radrajith/ESE_323_PCB_Design/Datasheets/4 pin connector/╨┬╜¿╬─╝■╝╨/CCF20160824.jpg

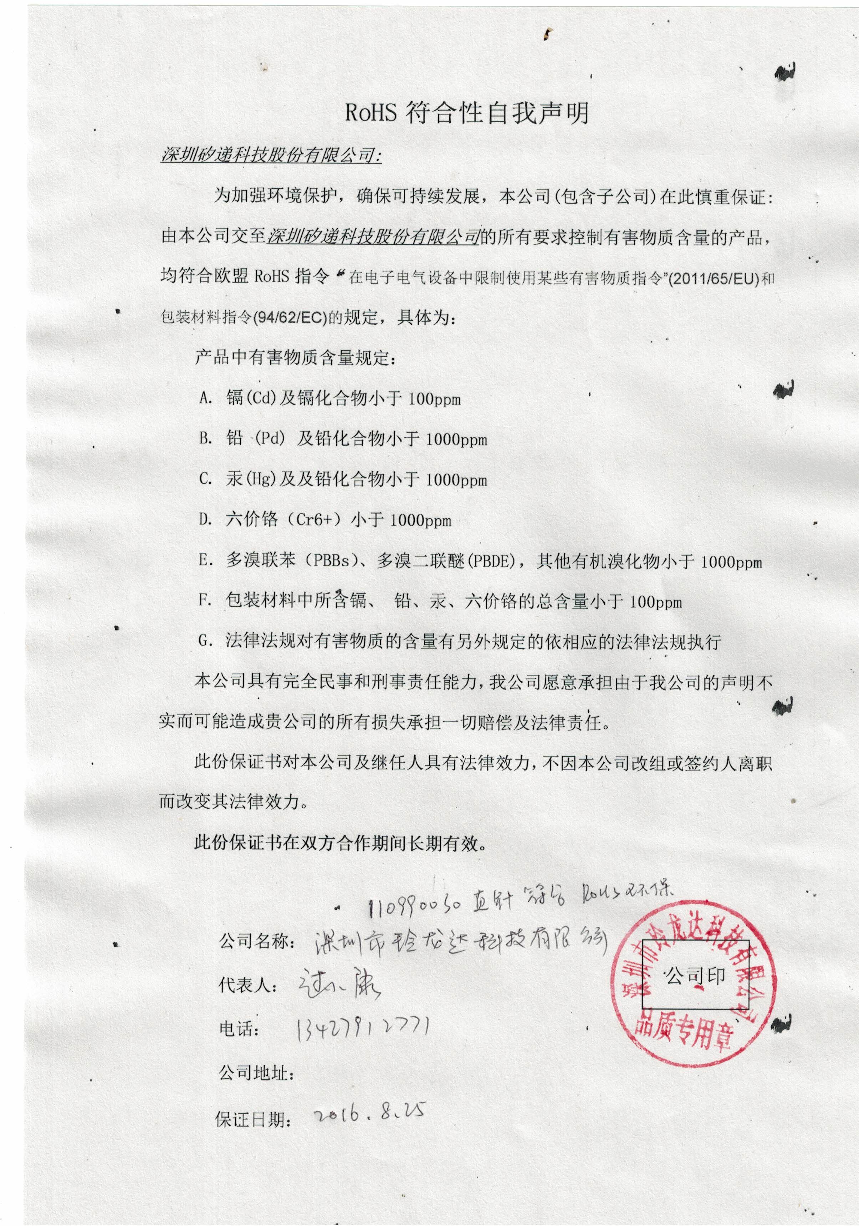
Datasheets/4 pin connector/╨┬╜¿╬─╝■╝╨/CCF20160824.jpg
