radrajith/ESE_323_PCB_Design/Pictures/4 terminal resistor.PNG

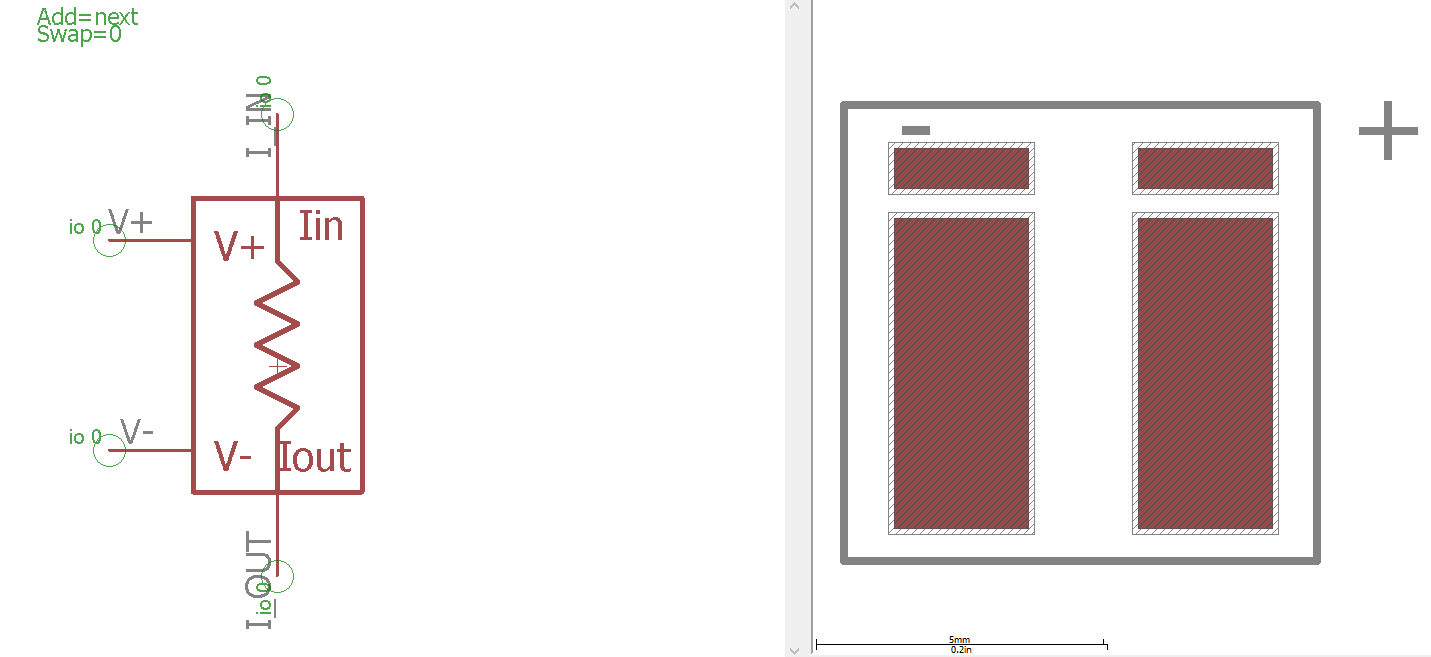
Pictures/4 terminal resistor.PNG
