radrajith/ESE_323_PCB_Design/Pictures/Atxmega/atxmega32.PNG

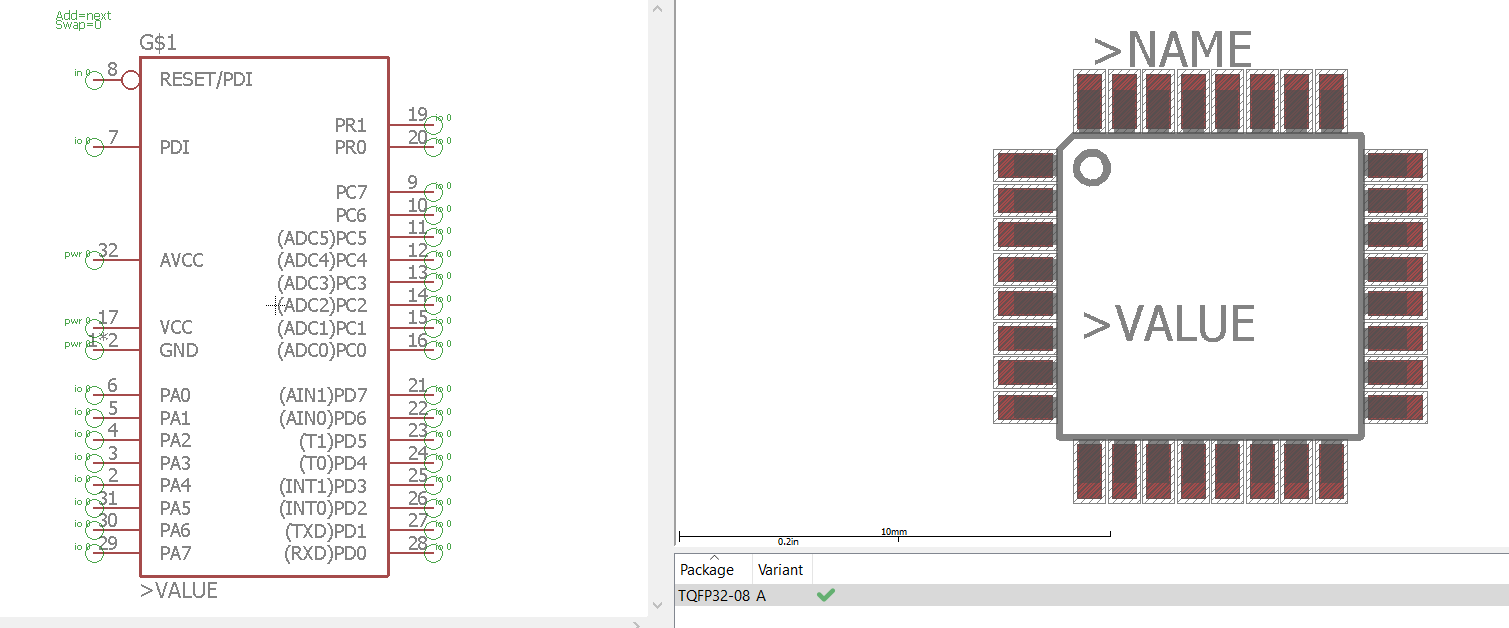
Pictures/Atxmega/atxmega32.PNG
