radrajith/ESE_323_PCB_Design/Pictures/Atxmega/pinouts.PNG

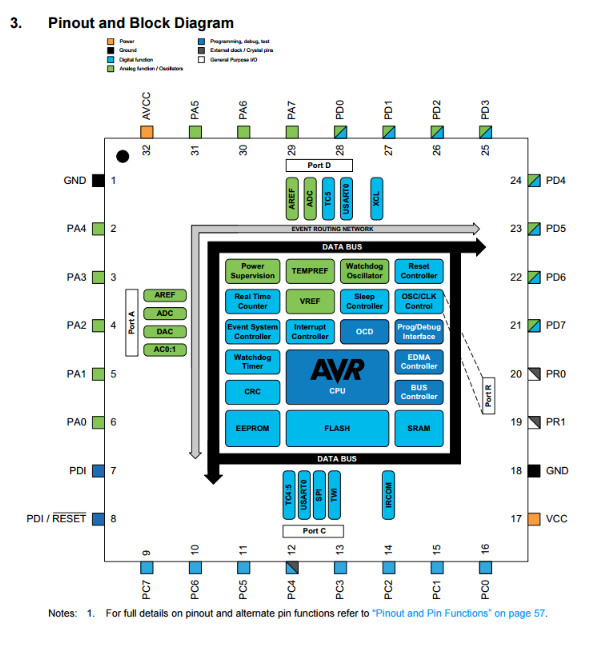
Pictures/Atxmega/pinouts.PNG
