radrajith/ESE_323_PCB_Design/Pictures/banana plug.PNG

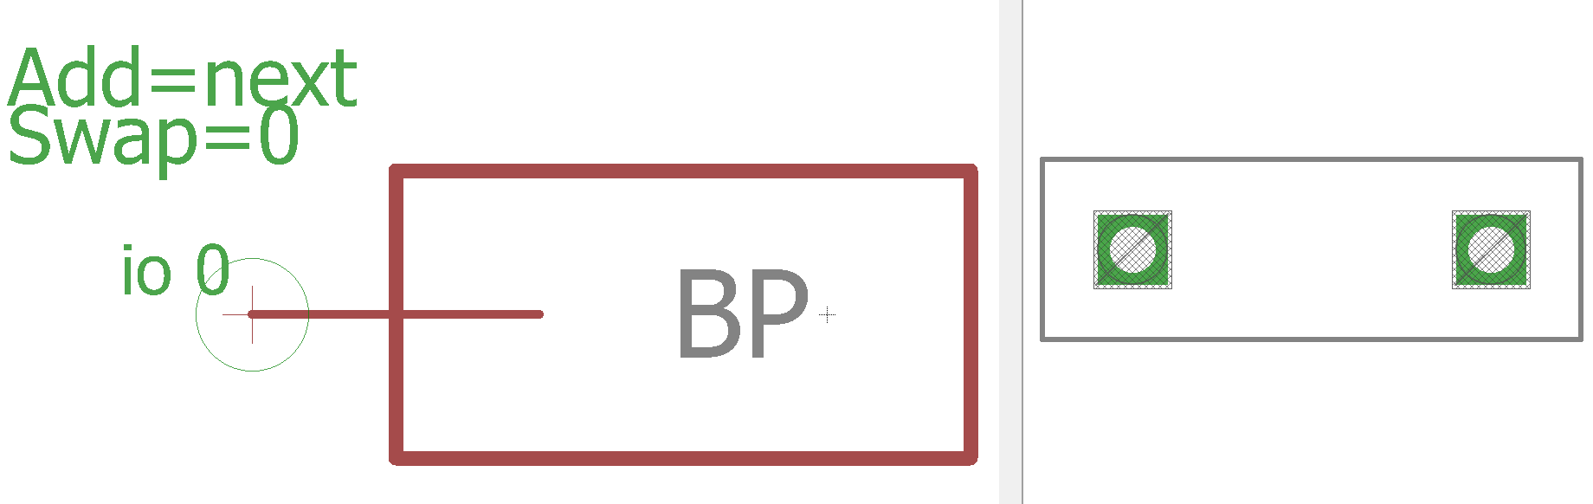
Pictures/banana plug.PNG
