radrajith/ESE_323_PCB_Design/Pictures/battery_case_Cad.PNG

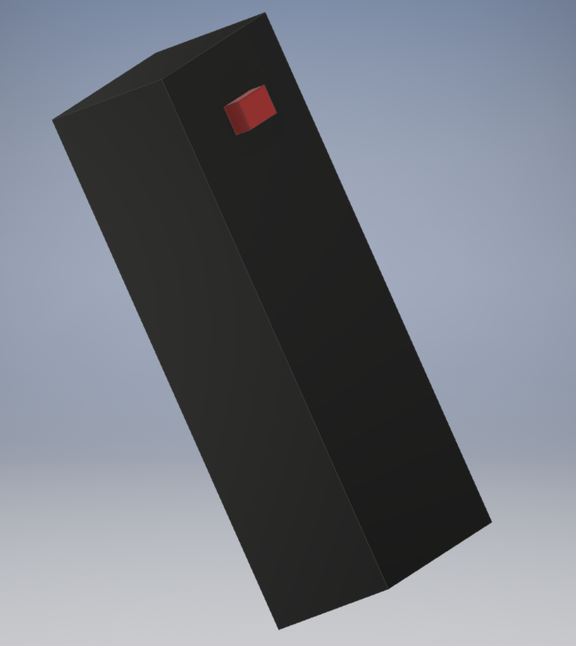
Pictures/battery_case_Cad.PNG
