radrajith/ESE_323_PCB_Design/Pictures/bottom_case.PNG

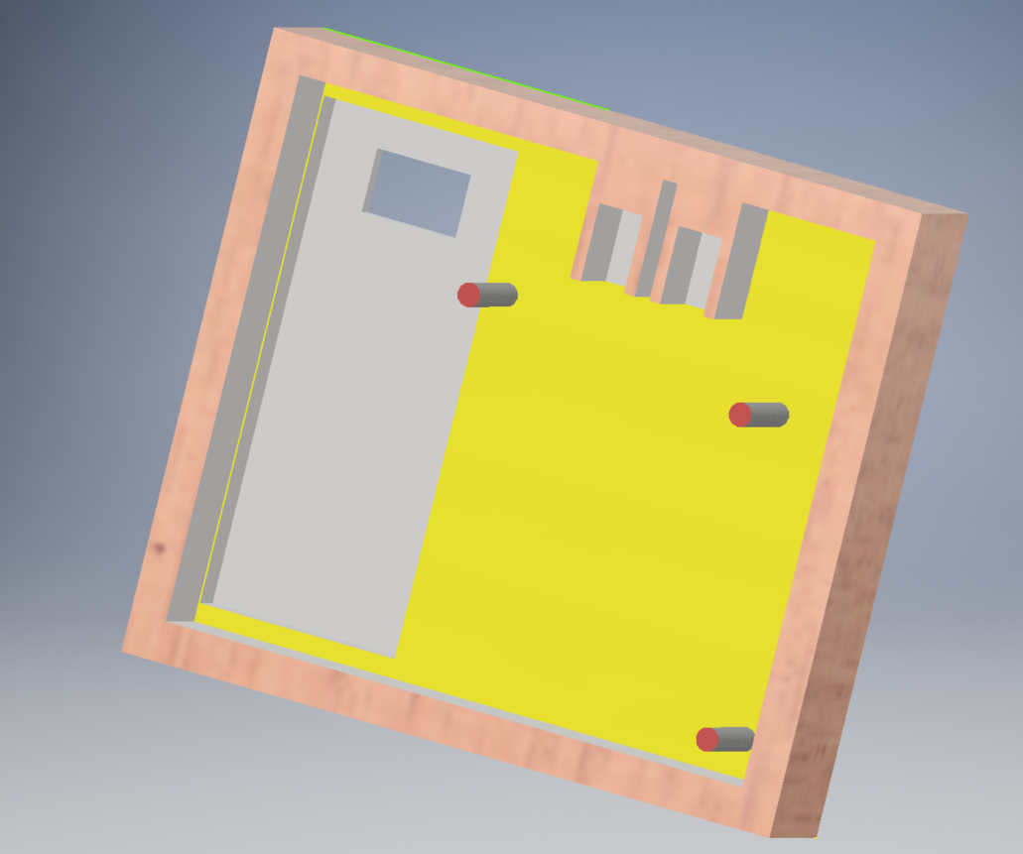
Pictures/bottom_case.PNG
