radrajith/ESE_323_PCB_Design/Pictures/button_press.PNG

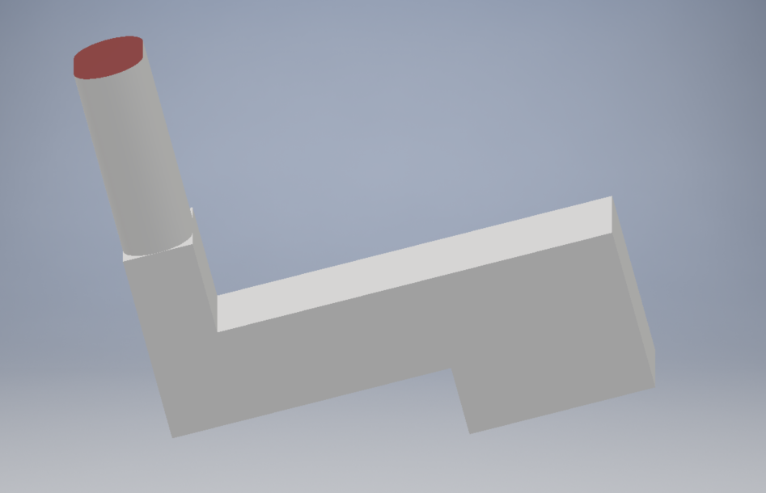
Pictures/button_press.PNG
