radrajith/ESE_323_PCB_Design/Pictures/jtag.PNG

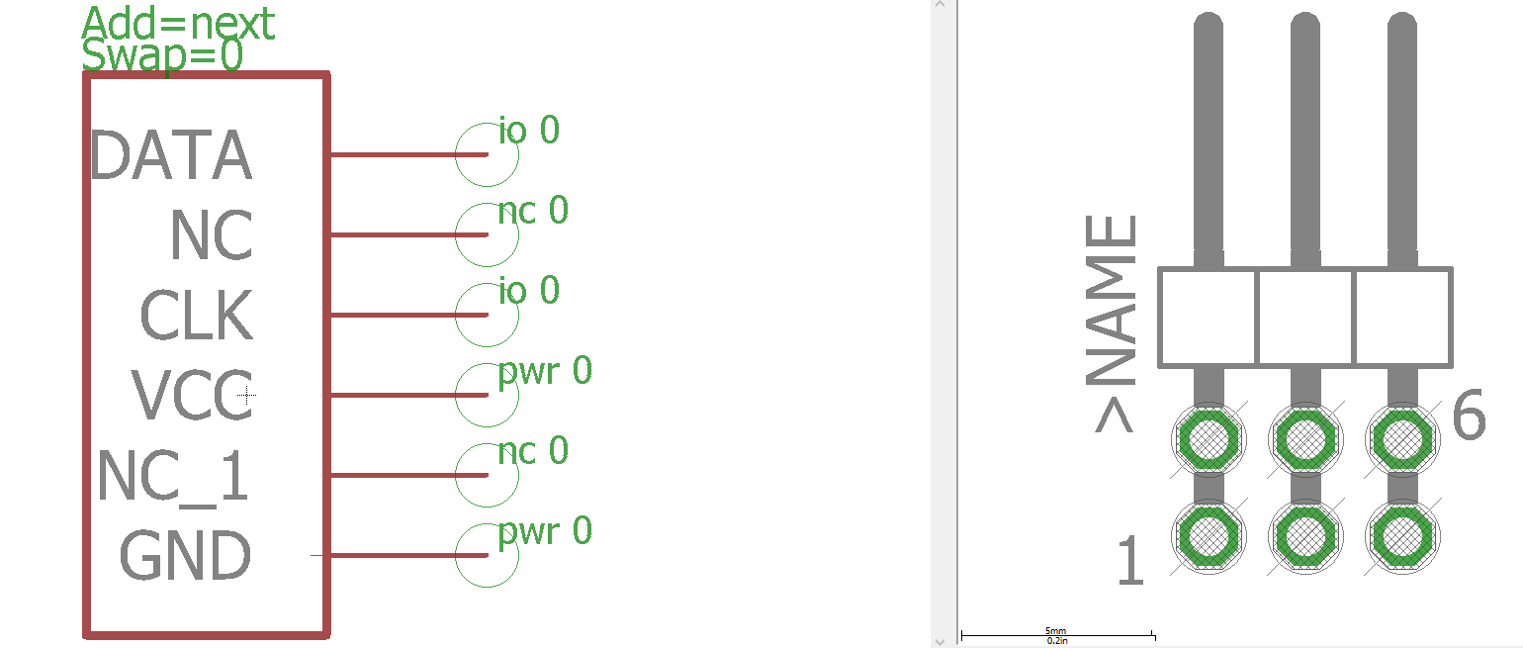
Pictures/jtag.PNG
