radrajith/ESE_323_PCB_Design/Pictures/LCD TFT screen/back_view.jpg

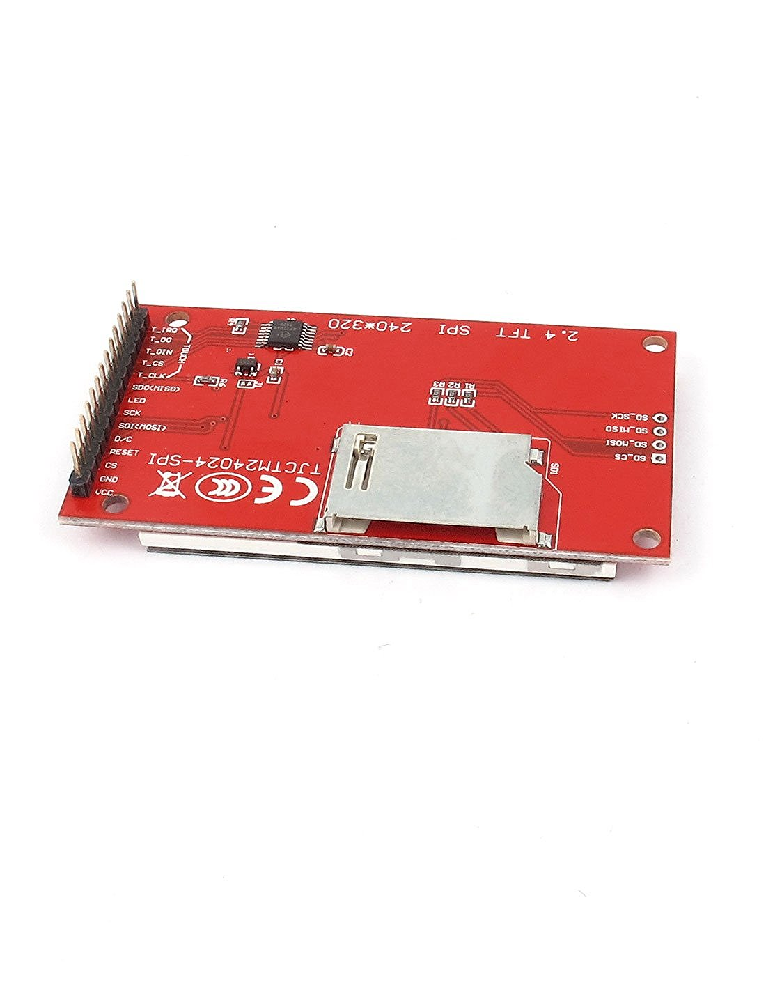
Pictures/LCD TFT screen/back_view.jpg
