radrajith/ESE_323_PCB_Design/Pictures/LCD TFT screen/Female header pins.PNG

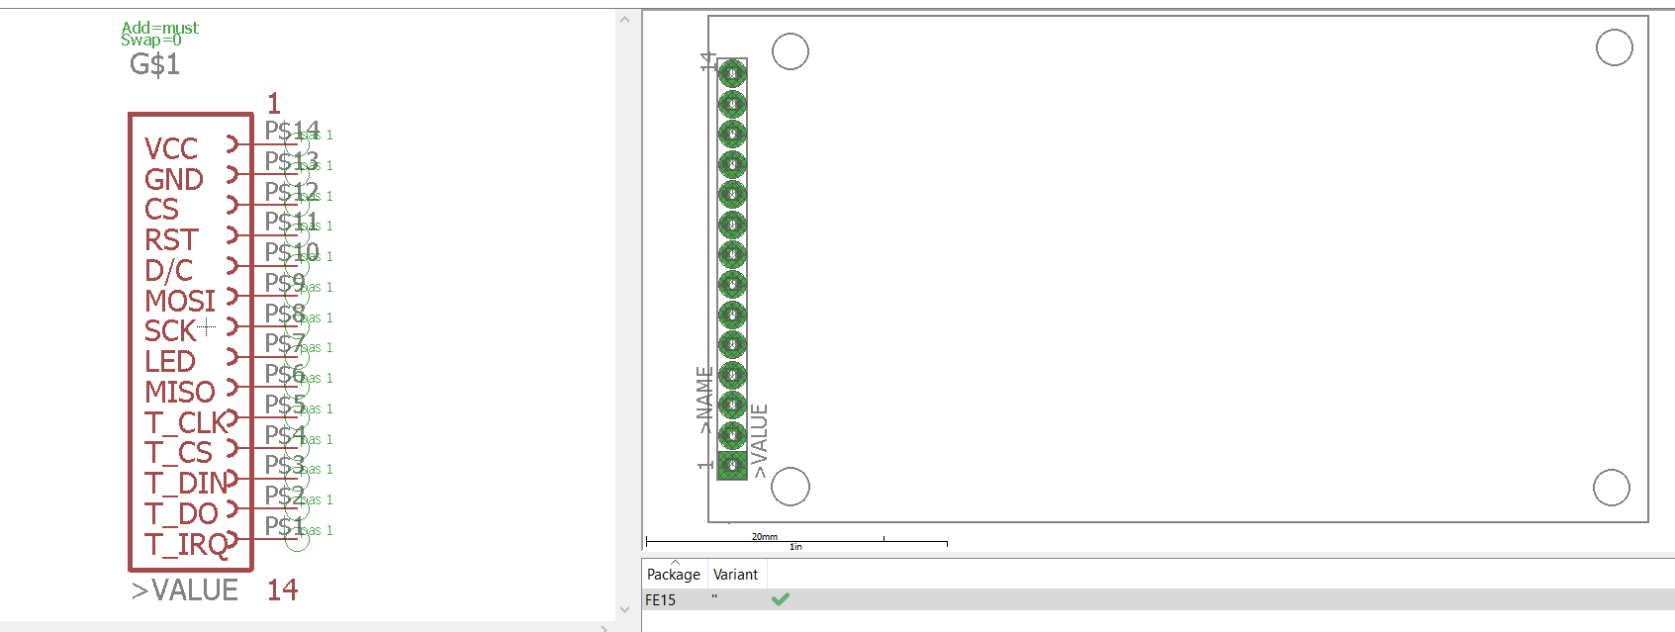
Pictures/LCD TFT screen/Female header pins.PNG
