radrajith/ESE_323_PCB_Design/Pictures/LCD TFT screen/front_view.jpg

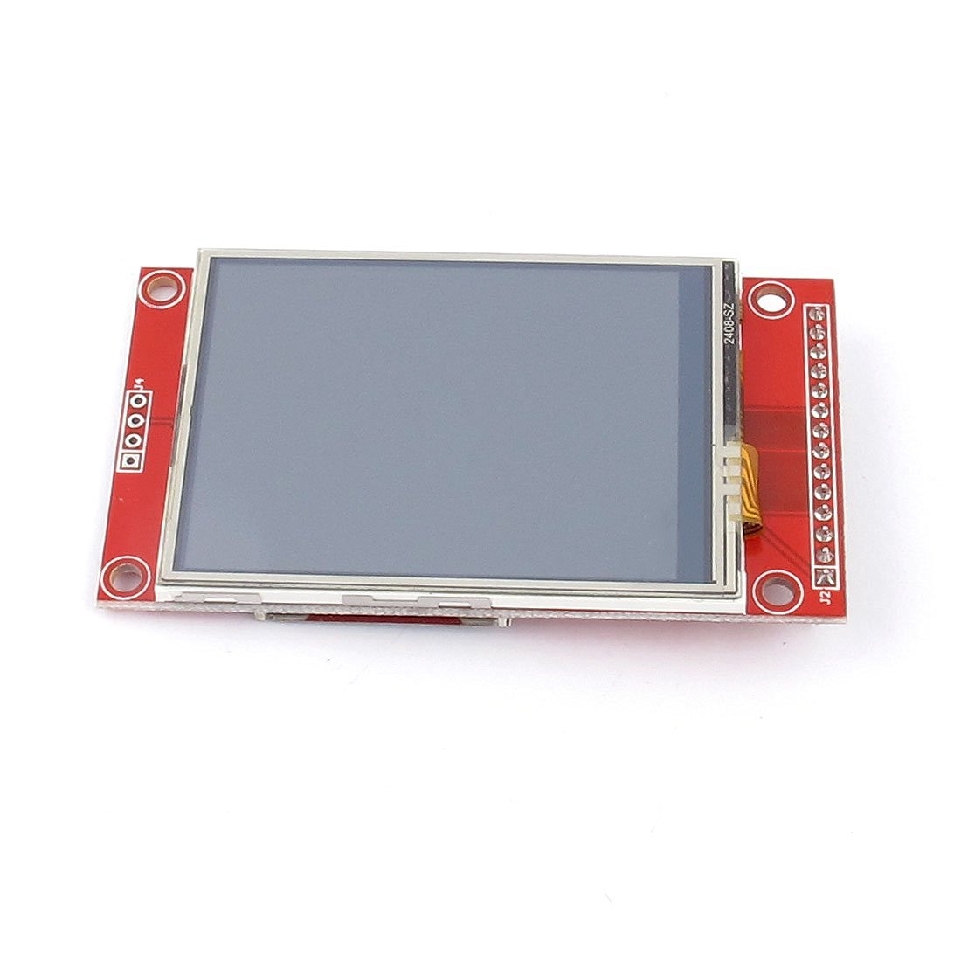
Pictures/LCD TFT screen/front_view.jpg
