radrajith/ESE_323_PCB_Design/Pictures/lcd_display_cad.PNG

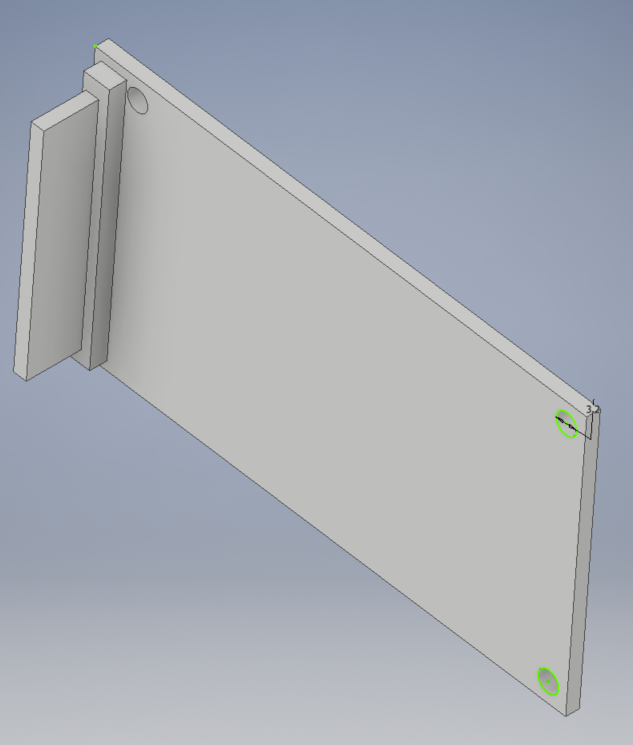
Pictures/lcd_display_cad.PNG
