radrajith/ESE_323_PCB_Design/Pictures/micro usb.PNG

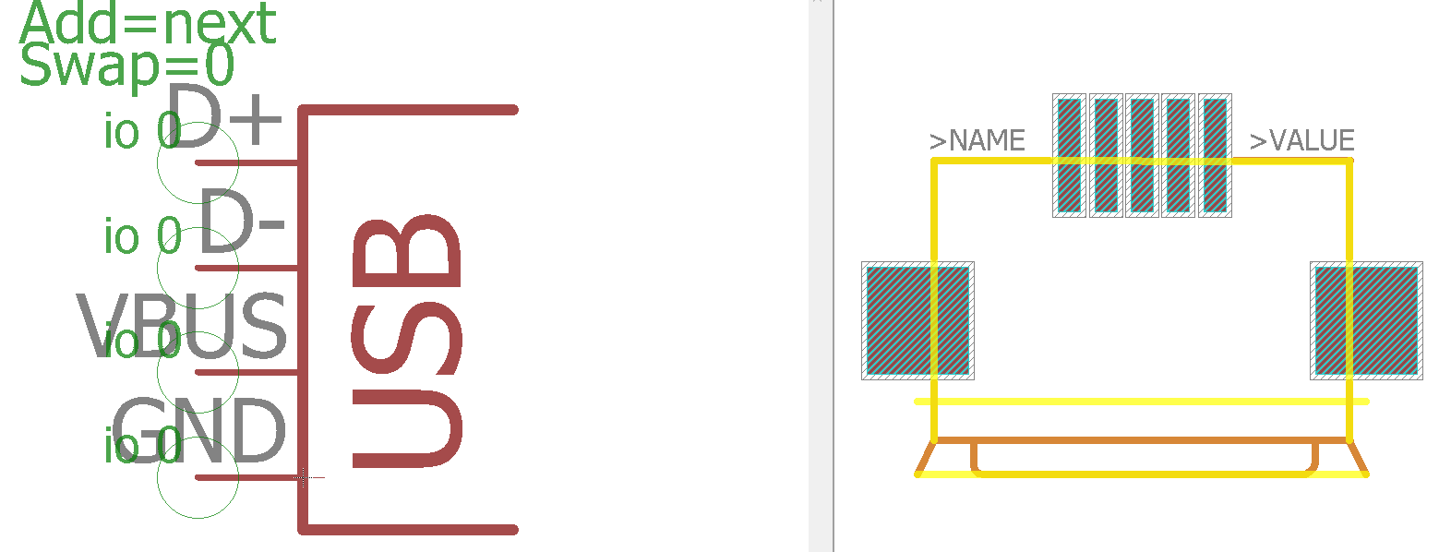
Pictures/micro usb.PNG
