radrajith/ESE_323_PCB_Design/Pictures/RGB LCD/universal 4 pin connector.PNG

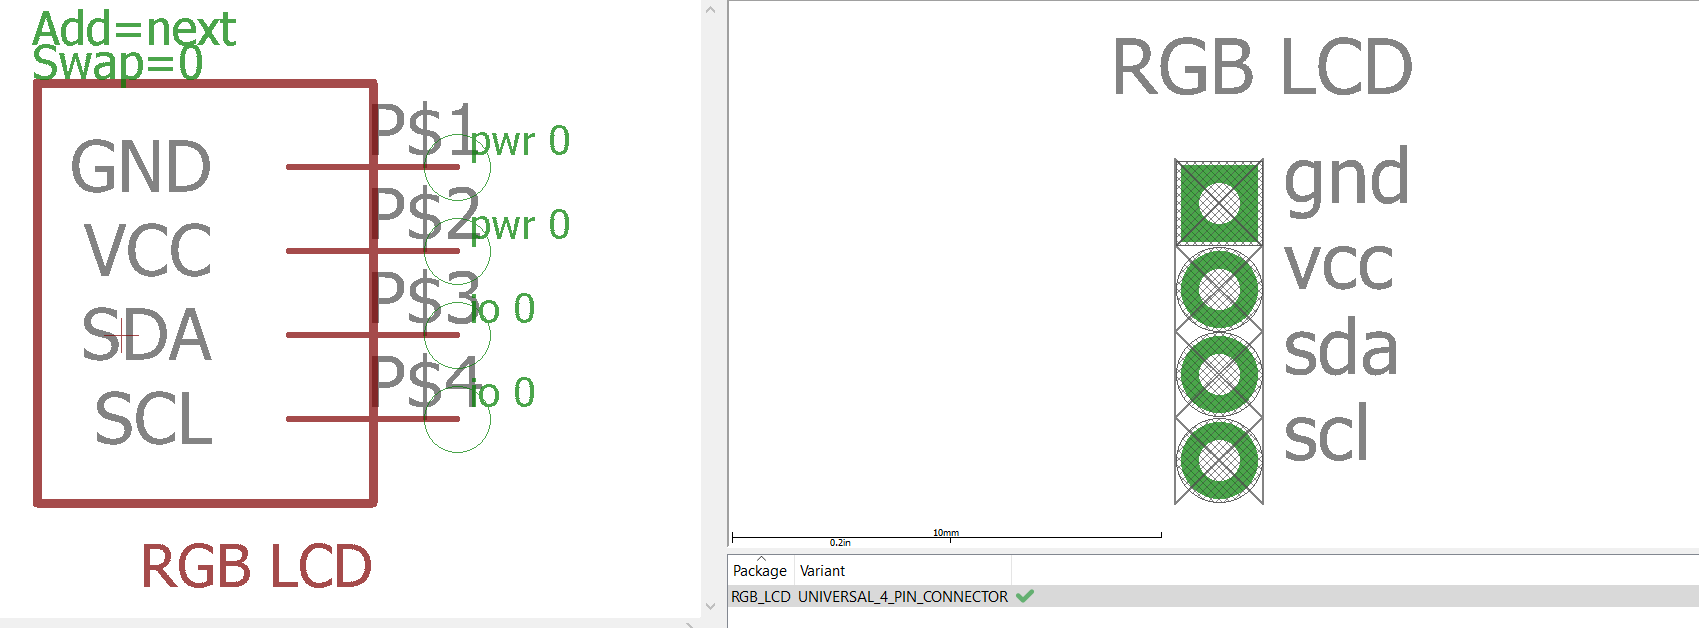
Pictures/RGB LCD/universal 4 pin connector.PNG
