radrajith/ESE_323_PCB_Design/Pictures/usbpic.PNG

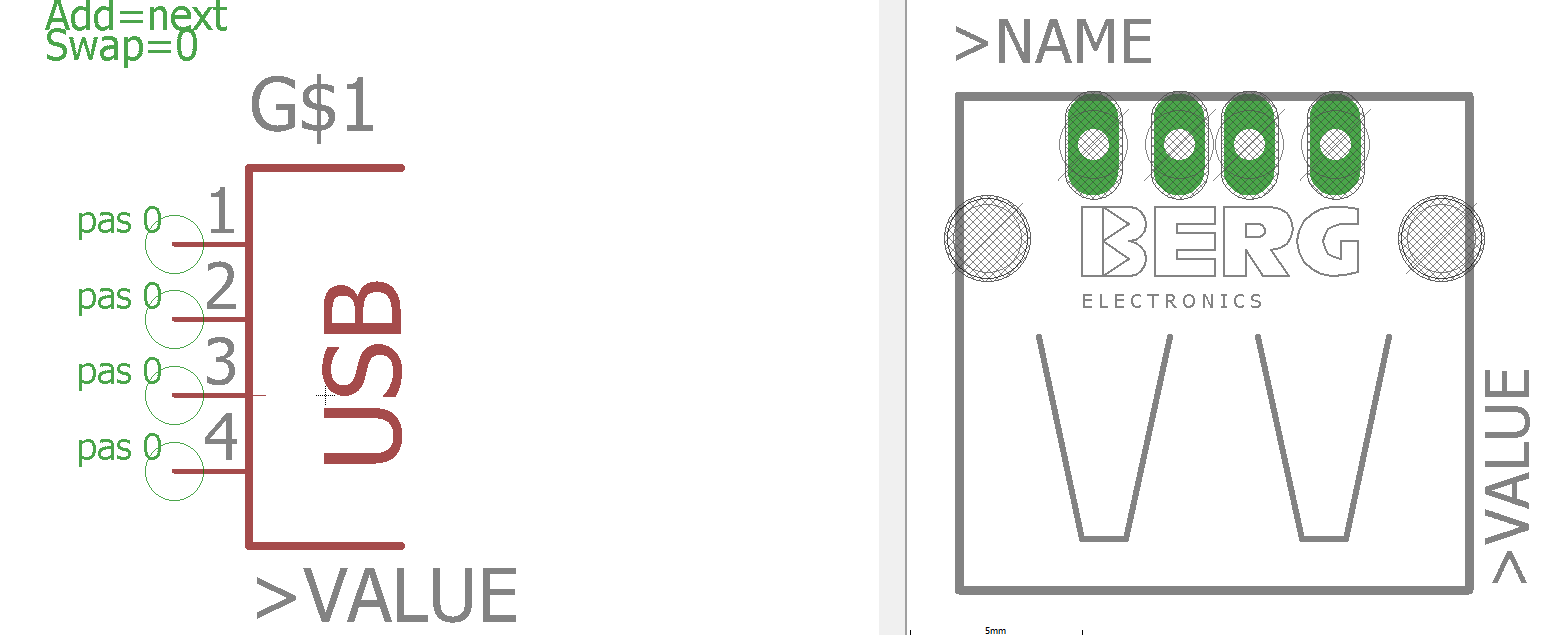
Pictures/usbpic.PNG
