radrajith/ESE_323_PCB_Design/Pictures/assembly_1_cad.PNG

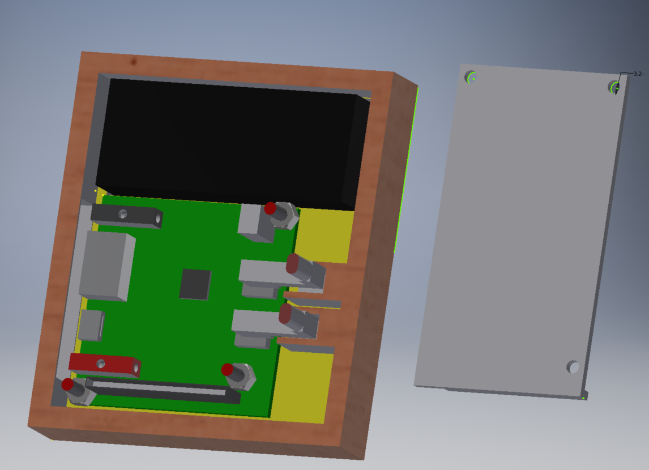
Pictures/assembly_1_cad.PNG
