radrajith/ESE_323_PCB_Design/TPS63000/Eagle/SPS/2016-10-14_05-18-27.sch

## EAGLE design TPS63000/Eagle/SPS/2016-10-14_05-18-27.sch (2016-10-21)

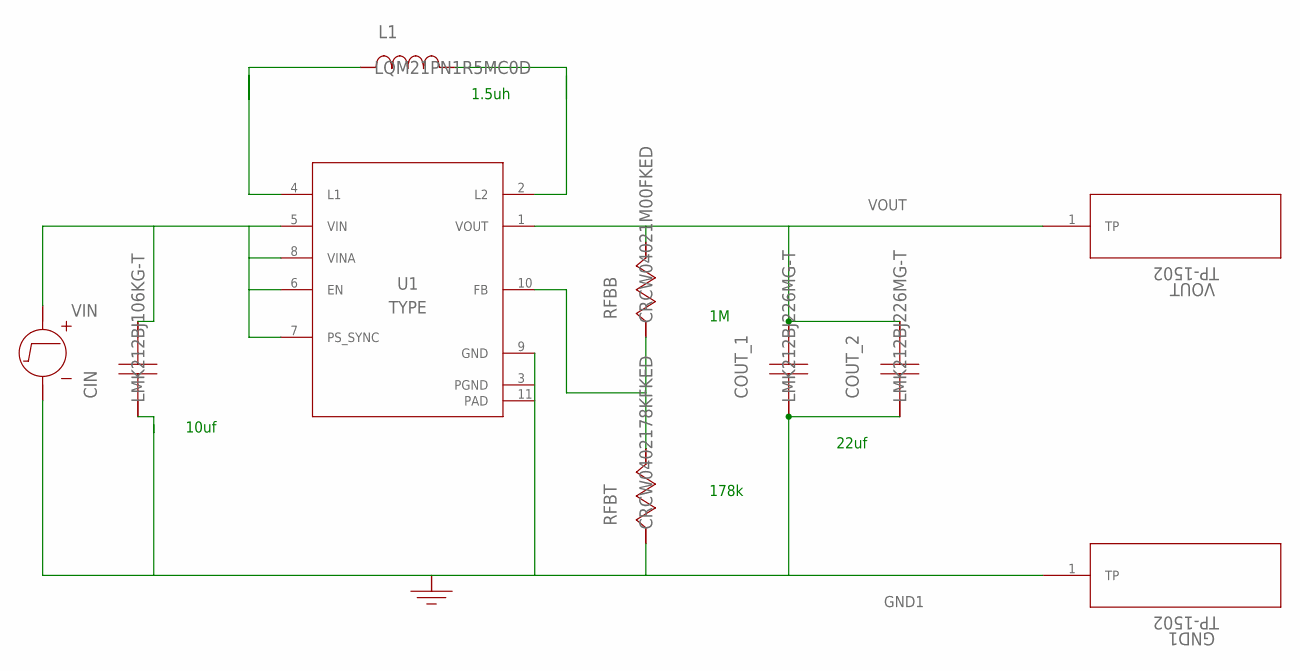
[picture p96: schematic 2016-10-14_05-18-27.sch]

Parts:
CIN: LMK212BJ106KG-T; 0805
COUT_1, COUT_2: LMK212BJ226MG-T; 0805
GND: WB_GND
GND1: TP-1502
L1: LQM21PN1R5MC0D; 0805
RFBB: CRCW04021M00FKED; 0402
RFBT: CRCW0402178KFKED; 0402
U1: TPS63000DRCR; DRC0010J
VIN: WB_STARTUP_VOLTAGE_SOURCE
VOUT: TP-1502

Connections:
1: CIN.1, U1.5 (VIN), U1.7 (PS_SYNC), U1.8 (VINA), VIN.1 (+)
2: L1.1, U1.4 (L1)
3: RFBB.2, RFBT.1, U1.10 (FB)
4: L1.2, U1.2 (L2)
GND1: CIN.2, COUT_1.2, COUT_2.2, GND.1, GND1.1, U1.3 (PGND), U1.9 (GND), U1.11 (PAD), VIN.2 (-)
VOUT: COUT_1.1, COUT_2.1, U1.1 (VOUT), VOUT.1

Notes on the sheet:
10uf
22uf
1.5uh
178k
