radrajith/ESE_323_PCB_Design/TPS63000/Eagle/sps/2016-10-14_05-17-29.sch

## EAGLE design TPS63000/Eagle/sps/2016-10-14_05-17-29.sch (2016-10-20)

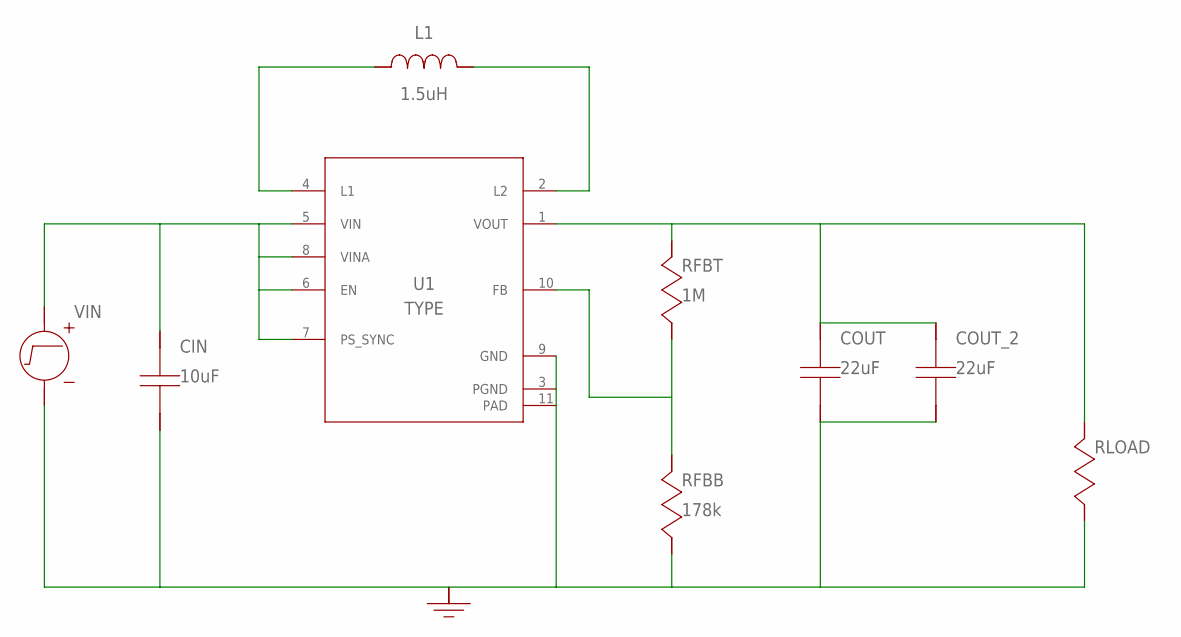
[picture p97: schematic 2016-10-14_05-17-29.sch]

Parts:
CIN: 10uF; 0805
COUT: 22uF; 0805
COUT_2: 22uF; 0805
GND: WB_GND
L1: 1.5uH; 0805
RFBB: 178k; 0402
RFBT: 1M; 0402
RLOAD: WB_LOAD_RESISTOR
U1: TPS63000DRCR; DRC0010J
VIN: WB_STARTUP_VOLTAGE_SOURCE

Connections:
0: CIN.2, COUT.2, COUT_2.2, GND.1, RFBB.2, RLOAD.2, U1.3 (PGND), U1.9 (GND), U1.11 (PAD), VIN.2 (-)
1: CIN.1, U1.5 (VIN), U1.6 (EN), U1.7 (PS_SYNC), U1.8 (VINA), VIN.1 (+)
2: L1.1, U1.4 (L1)
3: RFBB.1, RFBT.2, U1.10 (FB)
4: L1.2, U1.2 (L2)
6: COUT.1, COUT_2.1, RFBT.1, RLOAD.1, U1.1 (VOUT)
